dennisdobra/OpenBook-Project/Images/Back_Cover.png

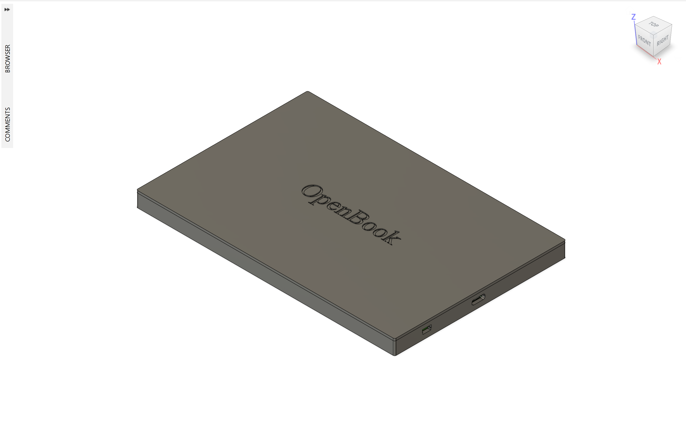
Images/Back_Cover.png
