dennisdobra/OpenBook-Project/Images/USB_Type_C_Port.png

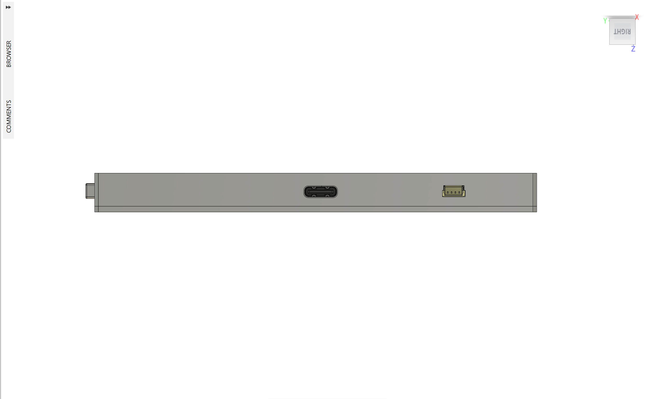
Images/USB_Type_C_Port.png
